Savio-Cardoz/Motas/Code/Motas/Motas/Motas_Controller.c

/**
* @Motas_Controller.c
* @brief this source file contains the implementation of the Application layer
  in the form of state machine
*
* @author Faisal Khan
*
* @date 29/05/2017
*/

/*===============================Includes=================================================*/
#include <avr/io.h>
#include <util/delay.h>
#include "Atmega_Config.h"
#include "Atmega_Uart.h"
#include "Peripheral_Drivers.h"
#include "Motas_Controller.h"
#include "debug_func.h"
#include "Dfplayer.h"
/*========================================================================================*/

/* All required flags in the application layer are present in this variable (8 per variable) */
reg flag_register_controller;		
/* Flag to indicate if the sd card is empty */
#define flag_sd_card_empty_g REGISTER_BIT(flag_register_controller, 0)
/* Flag to indicate if the music is playing */
#define flag_player_status_g REGISTER_BIT(flag_register_controller, 1)
#define flag_uss_state_g REGISTER_BIT(flag_register_controller, 2)	

/*===============================Global variables==========================================*/

/*Initialize the state machine to the INIT_STATE*/
static t_motascontroller_state motascontroller_state = MOTAS_INIT_STATE;

/* Holds the threshold value of the Ultrasonic sensor */
uint16_t threshold_uss_count = 0;

/* threshold uss count can be set different than normal. Delete if not required */
static uint16_t debug_threshold_uss_count = 0;
/*Demo value. Can be changed or can be kept as configurable*/
uint16_t threshold_pir_count = 1;

/*========================================================================================*/

/**
* This method is the state corresponding to the Initial state of the state machine
* @author Faisal Khan
* @param none
* @date 29/05/2017
*/
void Init_State(void)
{
	threshold_uss_count = 65535;
	
	// TODO: Add code to check the status of the DFplayer if a SD card is or isn't inserted
	if(Dfplayer_Query_Card_Presence())
	flag_sd_card_empty_g = True;
	else flag_sd_card_empty_g = False;
	// TODO: extern this flag. Please do not change the name
	if(True == flag_sd_card_empty_g)
	{
		#ifdef DEBUG_ON
			//TODO: Add a LED colour for information
		#endif

		motascontroller_state = MOTAS_DEBUGGING_STATE;	
	}

	//TODO: Check if any additional condition is required for this transition
	/* No debugging required. Start calibration */
	else
	{	
		motascontroller_state = MOTAS_CALIBRATION_STATE;	
	}
}


/**
* This method is the state corresponding to Ultrasonic calibration state where 
  Autocalibration of the ultrasonic is done and the value is stored in threshold_uss_count 
* @author Faisal Khan
* @param none
* @date 29/05/2017
*/
void Calibration_State(void)
{	
	/* Update the value of threshold*/
	_delay_ms(5000);
	threshold_uss_count = Get_Uss_Count();
	threshold_uss_count -= 200;
	
	#if DEBUG_ON
	SendDebug("USS calib");
	USART_Transmit_dec(threshold_uss_count);
	#endif
	/* Reset the PIR count*/
	Reset_Pir_count();
	
	#if DEBUG_ON
	/* Red led light for 1 second indicating calibration done and Motas entering the standy state */
	//DebugLedTransmit(LED_ON ,LED_RED);
	//_delay_ms(1000);
	//DebugLedTransmit(LED_OFF ,LED_RED);		/* Switch OFF the LED */
	#endif
	
	/* Update state */
	motascontroller_state = MOTAS_STANDBY_STATE;
	
	#if DEBUG_ON
	SendDebug("calib done");
	#endif
}

/**
* This method is the state corresponding to Ultrasonic standby state wherein values from 
  ultrasonic and PIR is checked continuously 
* @author Faisal Khan
* @param none
* @date 29/05/2017
*/
void Standby_State(void)
{
	uint16_t standby_pircount = 0;

	/* Update the PIR and ultrasonic count */
	standby_pircount = Get_Pir_count();

	DebugLedTransmit(LED_ON, LED_YELLOW);

	/*Check if Ultrasonic or pir has triggered because customer entering the room */
	if(flag_uss_state_g || (standby_pircount > 1))
	{
		DebugLedTransmit(LED_OFF ,LED_RED);
		flag_uss_state_g = False;
		/* Clear the standby pir count */
		standby_pircount = 0;
		
		/* Delay of 3 seconds to let the pir count increment */
		_delay_ms(3000);
		/* Read pir count*/
		standby_pircount = Get_Pir_count();

		/* Ignore uss count */
		if(standby_pircount > threshold_pir_count)
		{
			#if DEBUG_ON
			SendDebug("State changed : MOTAS ACTIVE");
			#endif
			motascontroller_state = MOTAS_ACTIVE_STATE;
		}
		/* Do nothing and stay in the current state */
		else 
		{
			#if DEBUG_ON
			SendDebug("State changed : MOTAS STANDBY");
			#endif
			motascontroller_state = MOTAS_STANDBY_STATE;
		}
	}
	/* Do nothing and stay in the current state */
	else
	{
		#if DEBUG_ON
		SendDebug("State changed : MOTAS STANDBY");
		#endif
		motascontroller_state = MOTAS_STANDBY_STATE;
	}
}


/**
* This method is the state corresponding to System Active state wherein music is started or 
  continued if already playing 
* @author Faisal Khan
* @param none
* @date 29/05/2017
*/
void Active_State(void)
{
	uint16_t active_pir_count = 0;
	/* Reset the USS flag	*/
	flag_uss_state_g = False;
	
	/* Play music */
	if(False == flag_player_status_g)
	{
		/* Change the status of music player to playing */
		flag_player_status_g = True;
		/* Play the first track */
		Dfplayer_Cmd(CMD_PLY_TRCK, 1);
	}
	else 
	{
		/* Do nothing */
	}

	///* Orange led light for 1 second indicating in the standy state */
	
	DebugLedTransmit(LED_OFF, LED_YELLOW);
	//_delay_ms(1000);
	//DebugLedTransmit(LED_OFF ,LED_ORANGE);		/* Switch OFF the LED */
	
	Reset_Pir_count();

	_delay_ms(5000);			// Default scan rate of the PIR requires 5 seconds before the next pulse is given
	
	/* Get pir count */
	active_pir_count = Get_Pir_count();
	
	/* Check if Customer present in the room */
	if((active_pir_count >= threshold_pir_count) && (!flag_uss_state_g))
	{
		/* Do not change the state. Keep audio playing*/
		motascontroller_state = MOTAS_ACTIVE_STATE;
	}
	/*Customer has left the room */
	else if(flag_uss_state_g)
	{
		DebugLedTransmit(LED_OFF ,LED_RED);
		flag_uss_state_g = False;
		/* Stop playing music */
		#if DEBUG_ON
		SendDebug("State changed MOTAS STOP PLaying");
		#endif
		Dfplayer_Cmd(CMD_PAUSE, 1);
		
		/* Change the status of music player to false(Music not playing) */
		flag_player_status_g = False;
		
		/* Change the state to standby state*/
		Reset_Pir_count();
		motascontroller_state = MOTAS_STANDBY_STATE;	
	}
	else motascontroller_state = MOTAS_ACTIVE_STATE;
	
}

/**
* This method is for the debugging state. Check if sensors are working as required.
* Note that no state would be changed after this
* @author Faisal Khan
* @param none
* @date 29/05/2017
*/
void Debugging_State(void)
{
	uint16_t pir_count = 0;
	uint16_t uss_count = 0;

	#if DEBUG_ON
	SendDebug("STATE : DEBUGGING");
	#endif
		
	/* Yellow led light indicating start of Debugging mode */
	DebugLedTransmit(LED_ON ,LED_YELLOW);
	_delay_ms(2000);
	
	/* Get the pir count */
	Reset_Pir_count();
	pir_count = Get_Pir_count();

	/* Get the USS count */
	uss_count = Get_Uss_Count();

	/* Check if pir is triggered */
	if(pir_count > 1)
	{
		/* Red led light indicating pir triggered */
		DebugLedTransmit(LED_ON, LED_RED);
		_delay_ms(2000);
	}
	/* Check if USS is triggered */
	else if(uss_count > debug_threshold_uss_count);
	{
		/* Orange led light indicating uss triggered */
		DebugLedTransmit(LED_ON, LED_ORANGE);
		_delay_ms(2000);
	}
}

/**
* This method is the main state machine function. This function would be called from the main func  
* @author Faisal Khan
* @param none
* @date 29/05/2017
*/
void MotasController(void)
{
	//TODO: Implement some timing delay if required 

	switch(motascontroller_state)
	{
		case MOTAS_INIT_STATE:
			Init_State();
			break;	

		case MOTAS_CALIBRATION_STATE:
			Calibration_State();
			break;	

		case MOTAS_STANDBY_STATE:
			Standby_State();
			break;

		case MOTAS_ACTIVE_STATE:
			Active_State();
			break;

		case MOTAS_DEBUGGING_STATE:		
			Debugging_State();	
			break;

		default : 
			/*Do nothing*/
			break;	

	}
}
